kraakenstuff/Skis/art/crunch.png

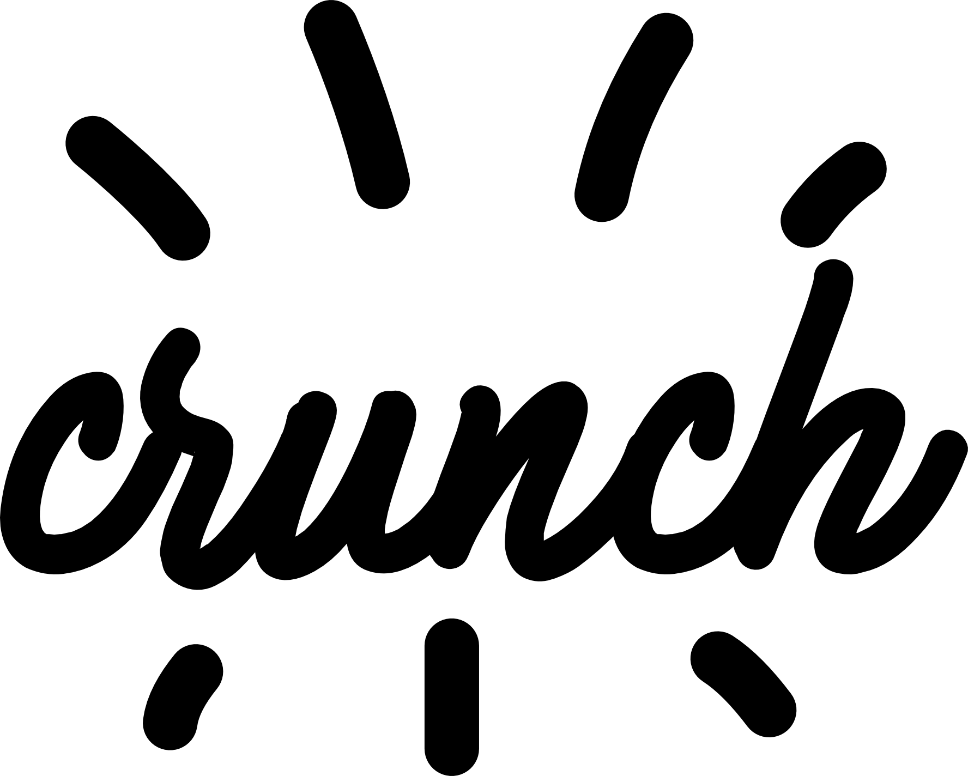
art/crunch.png
