kraakenstuff/Skis/art/cv1.png

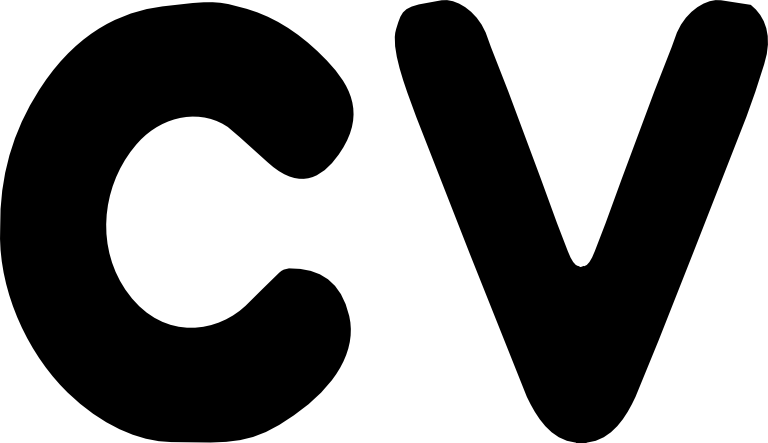
art/cv1.png
