kraakenstuff/Skis/art/cv.png

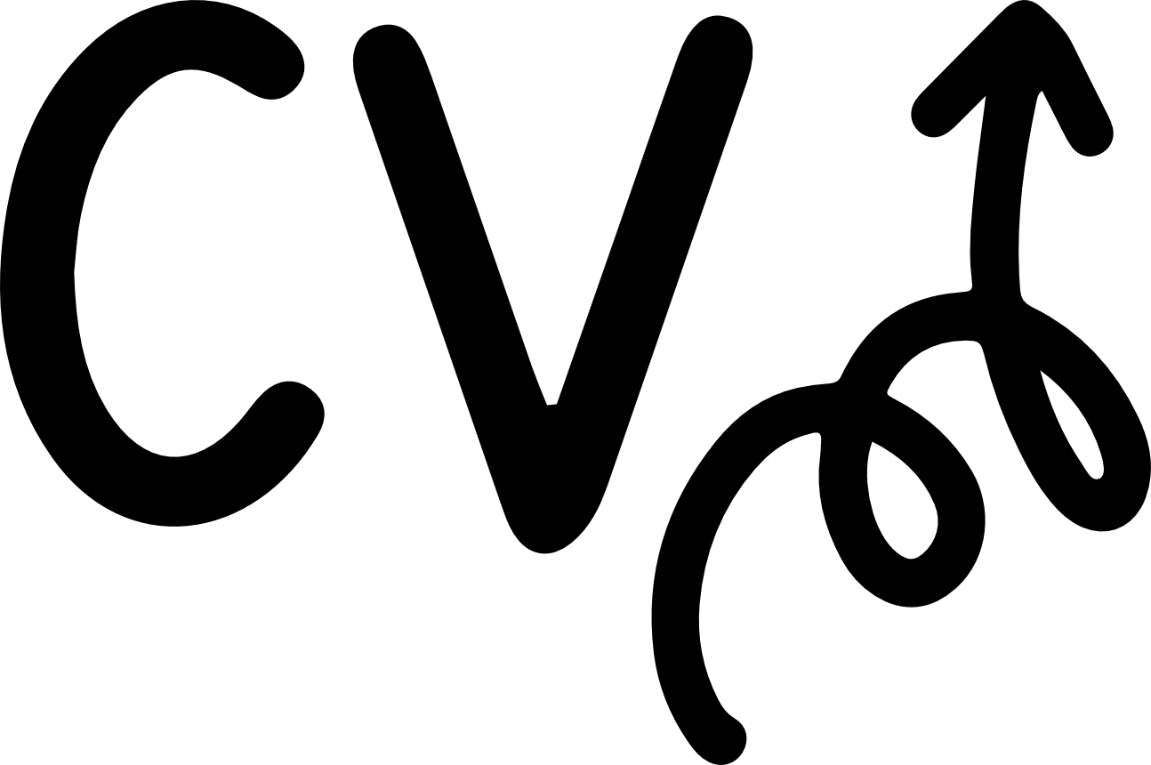
art/cv.png
