kraakenstuff/Skis/art/decay.png

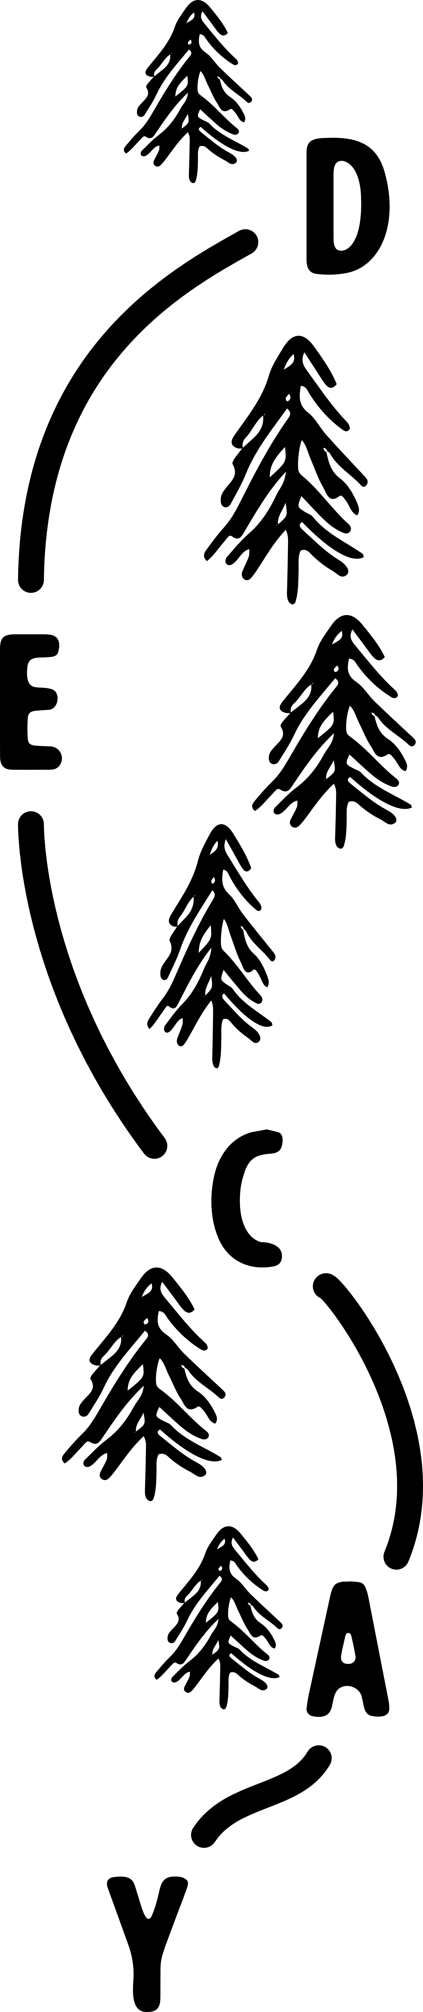
art/decay.png
