kraakenstuff/Skis/art/in.png

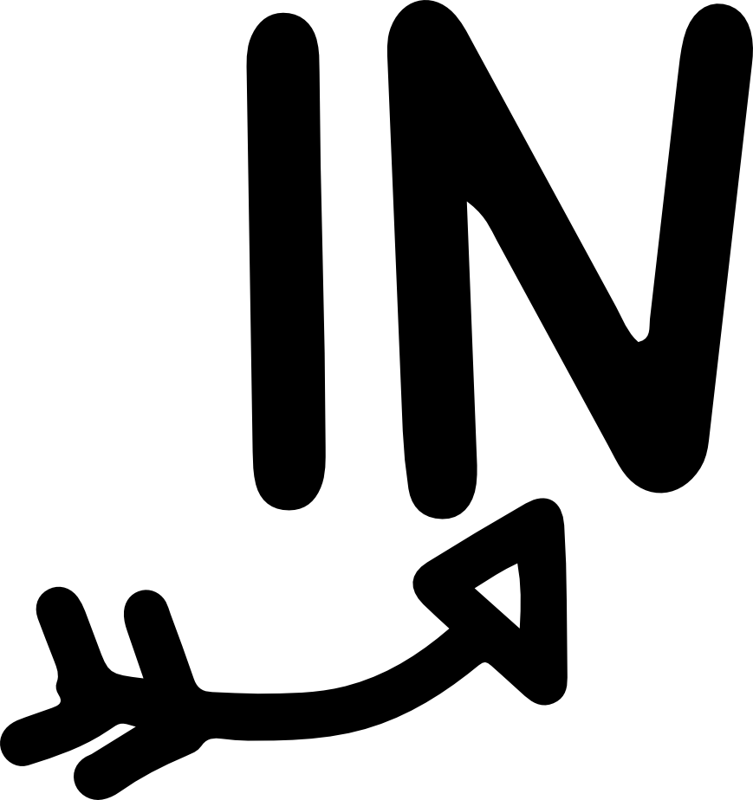
art/in.png
