kraakenstuff/Skis/art/kraakenstuff.png

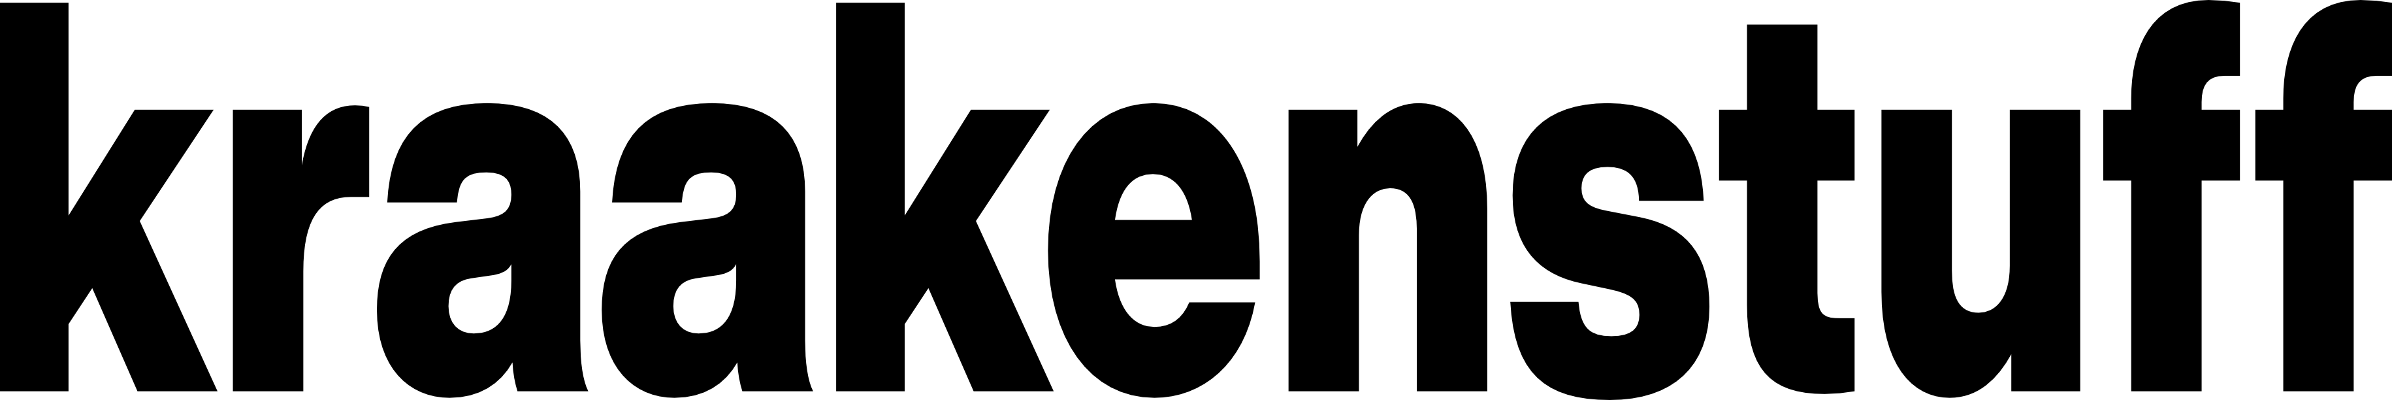
art/kraakenstuff.png
