kraakenstuff/Skis/art/out.png

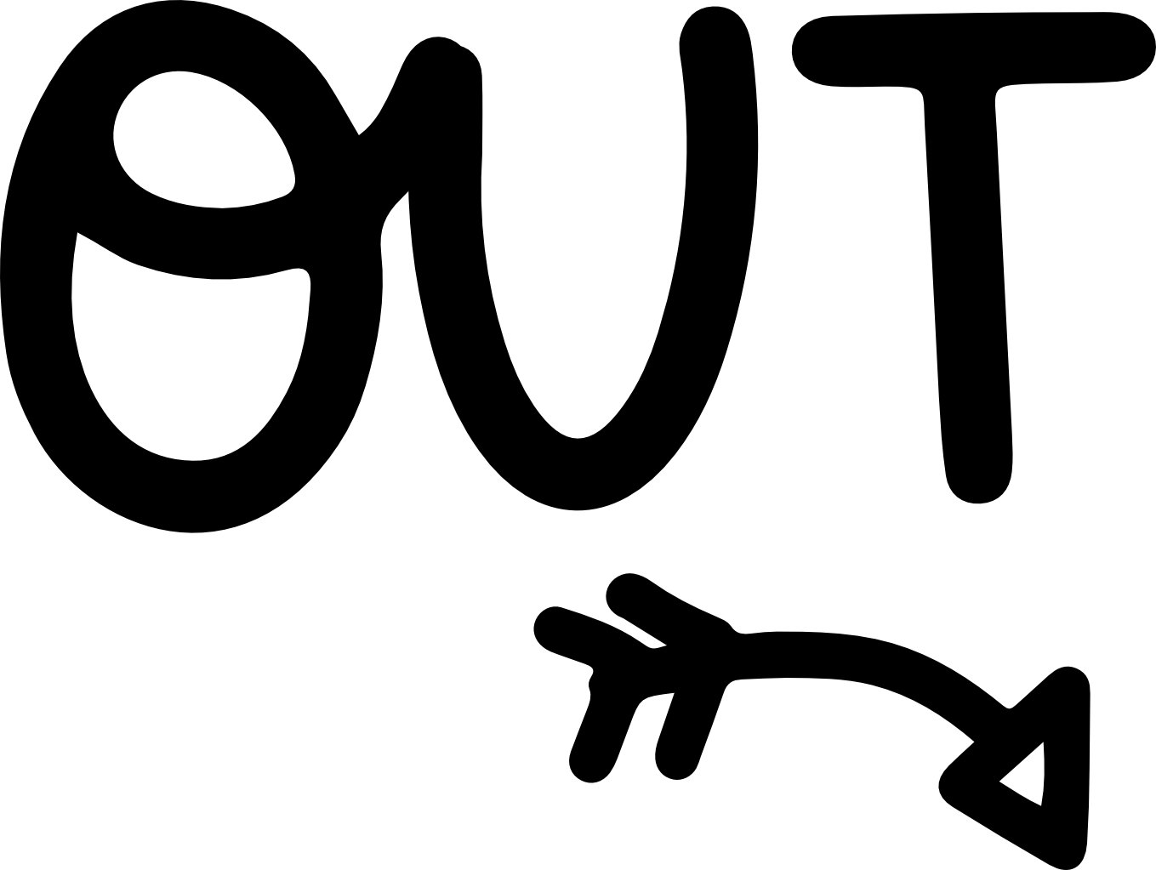
art/out.png
