kraakenstuff/Skis/art/range.png

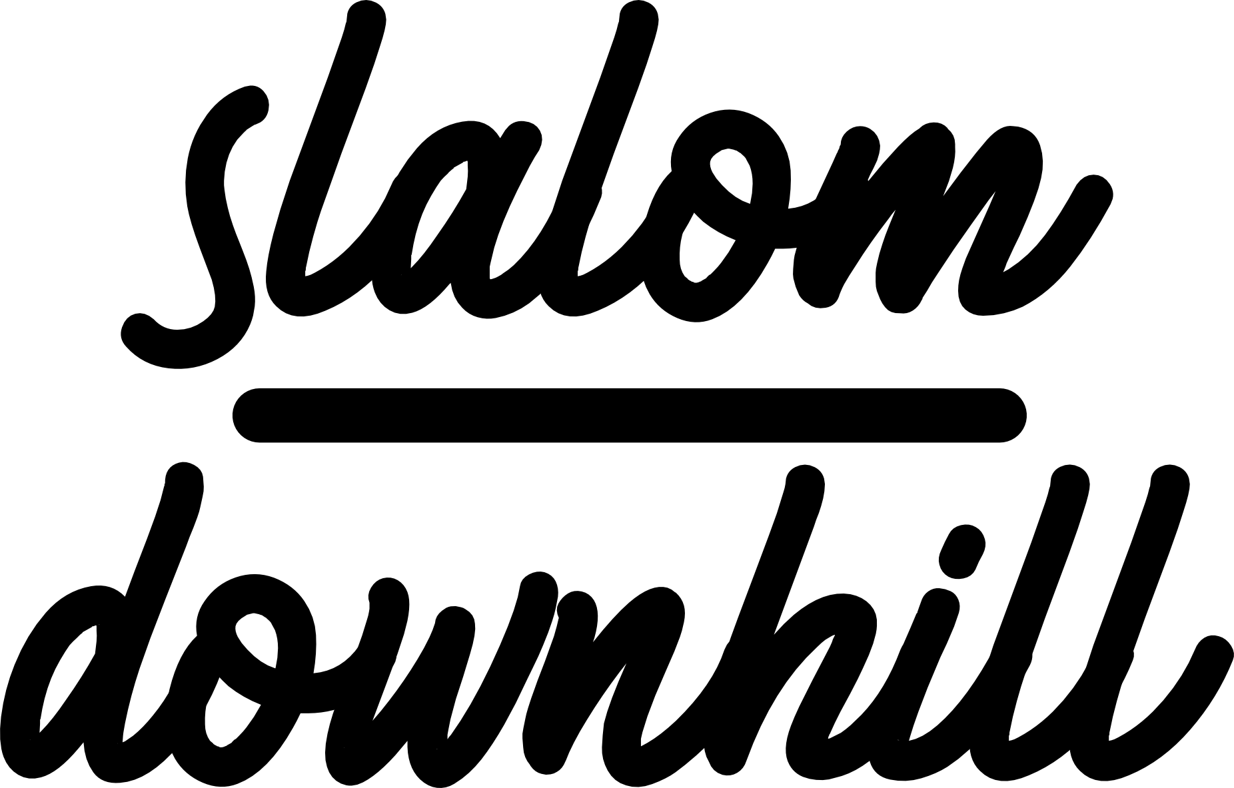
art/range.png
