kraakenstuff/Skis/art/Skis.png

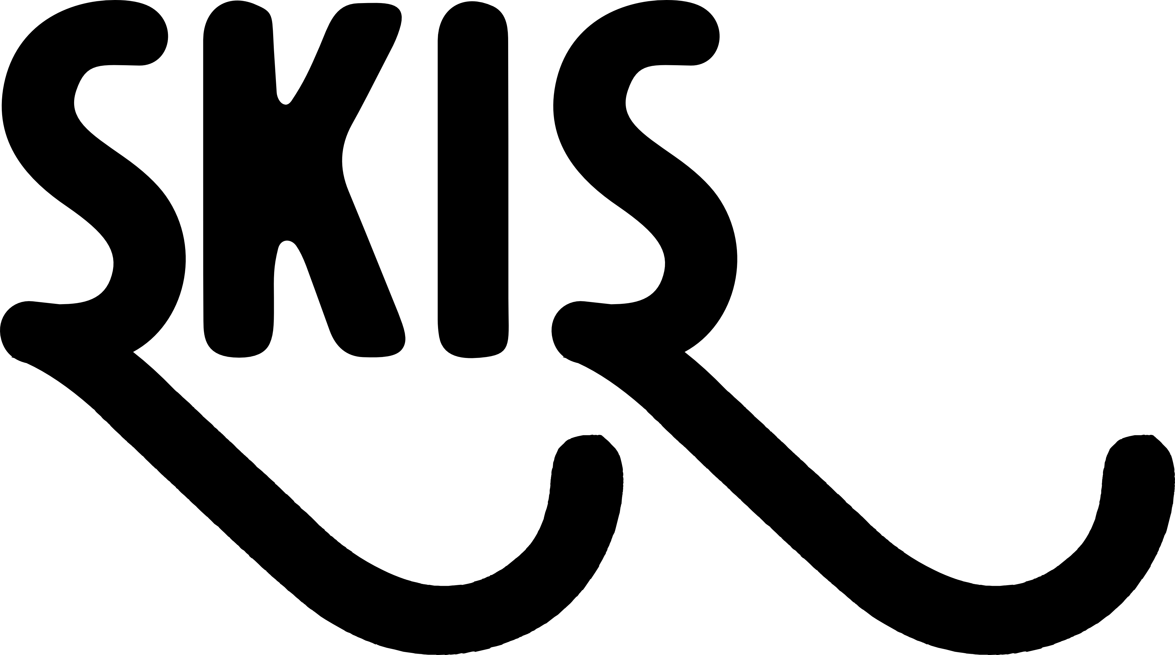
art/Skis.png
