kraakenstuff/Skis/art/snowflake.png

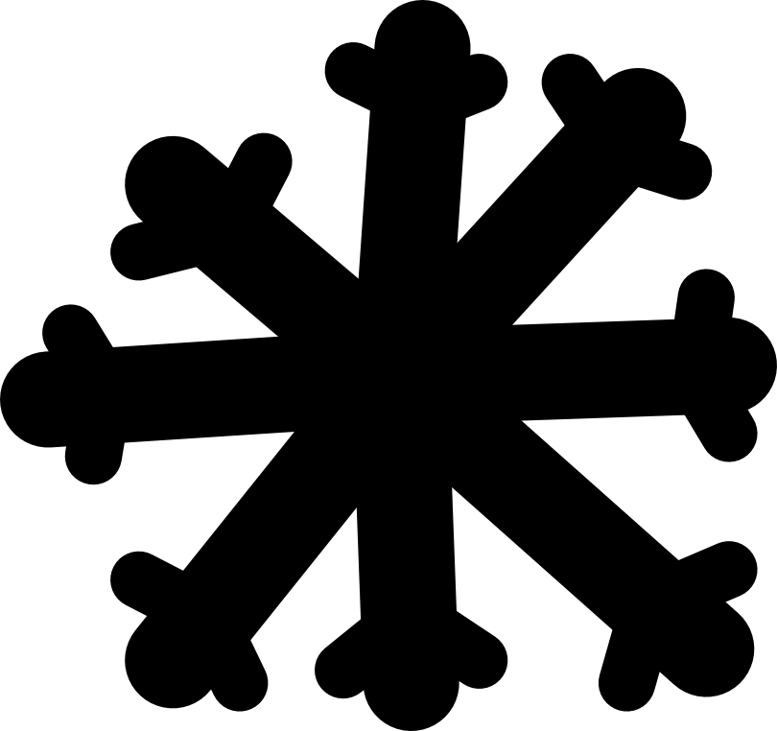
art/snowflake.png
