kraakenstuff/Skis/art/trig.png

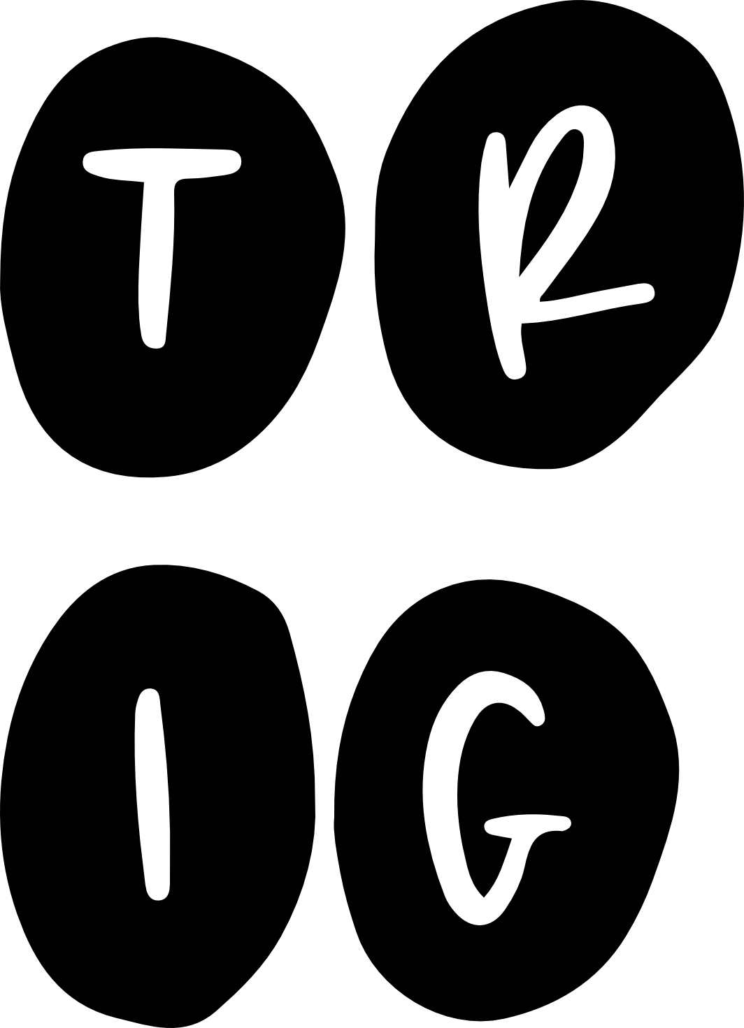
art/trig.png
